laurent-fr/z180/enclosure/lasercut/bolt.dxf

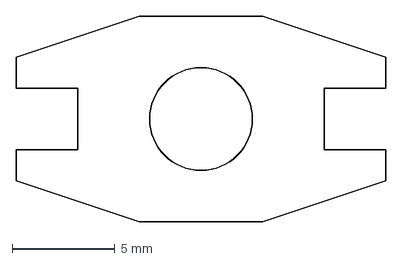
[picture p16: CAD file, 2020-05-03]
enclosure/lasercut/bolt.dxf
18.0 x 10.0 mm
