laurent-fr/z180/hardware/mio/sound/ltspice/Draft1.asc

C1: cap; 10n
R1: res; 1K
R3: res; 100K
U1: LT1677
V1: voltage; 12
V2: voltage; PWL file=C:\Users\Laurent\Desktop\out.pwl
Named nets: 0
.tran 0.04
